JuanCruzz7/Sistema_de_deteccion_de_accidentes_vehiculares/Sistema de detección de accidentes vehiculares/Imágenes/6 - Implementación de pack de baterías.jpeg

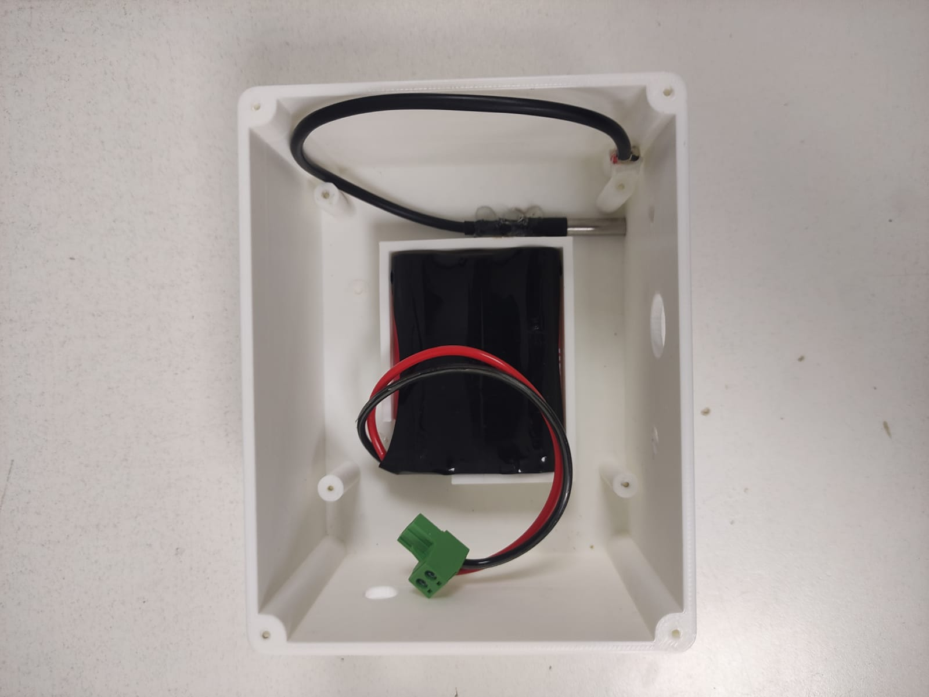
Sistema de detección de accidentes vehiculares/Imágenes/6 - Implementación de pack de baterías.jpeg
