JuanCruzz7/Sistema_de_deteccion_de_accidentes_vehiculares/Sistema de detección de accidentes vehiculares/Imágenes/10 - Comunicación serie - segundo prototipo de PCB.jpeg

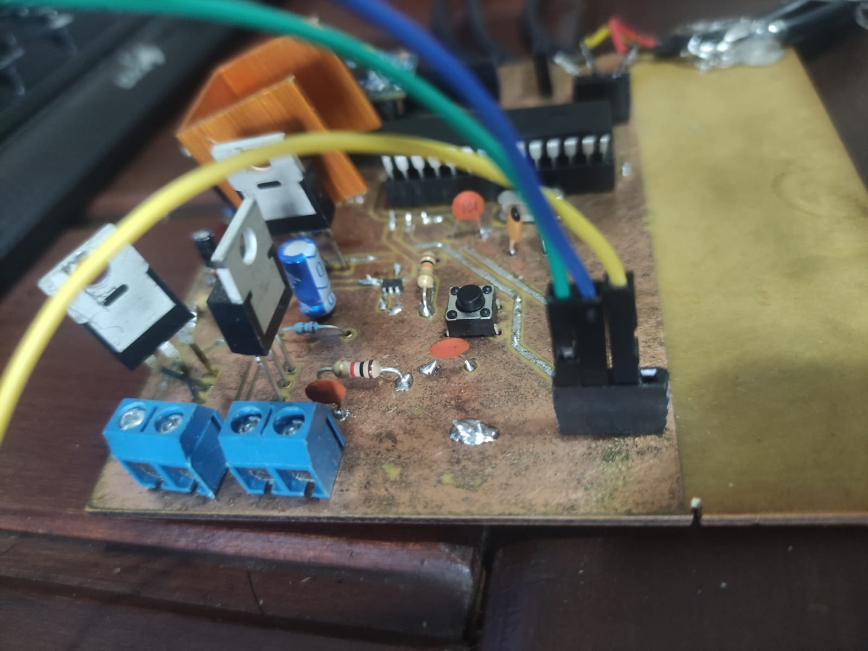
Sistema de detección de accidentes vehiculares/Imágenes/10 - Comunicación serie - segundo prototipo de PCB.jpeg
