JuanCruzz7/Sistema_de_deteccion_de_accidentes_vehiculares/Sistema de detección de accidentes vehiculares/Imágenes/13 - Antena GPS.jpeg

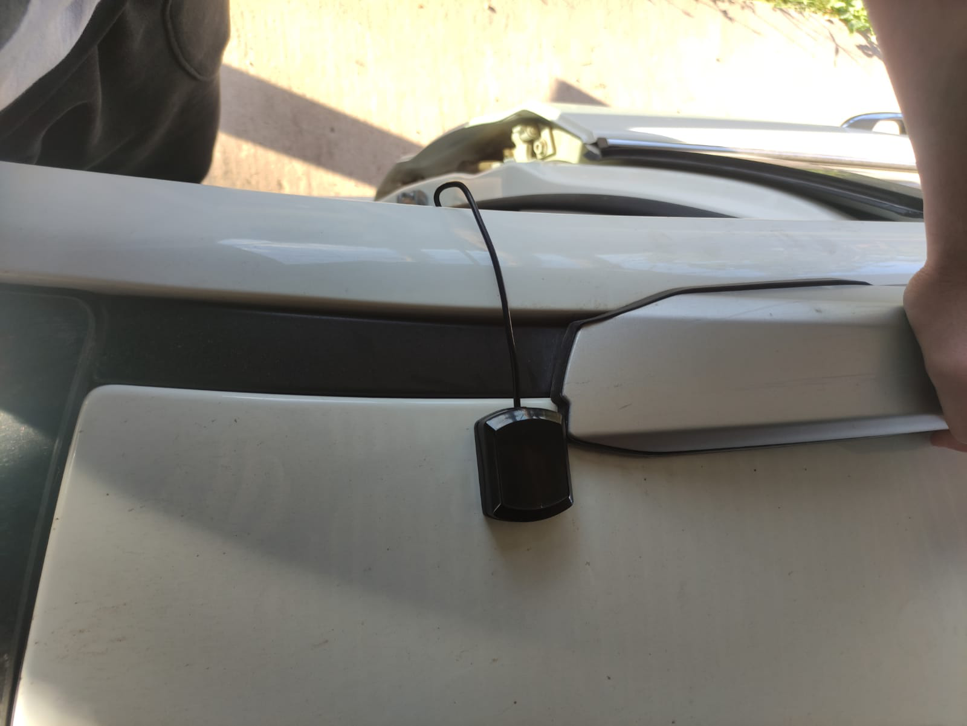
Sistema de detección de accidentes vehiculares/Imágenes/13 - Antena GPS.jpeg
