JuanCruzz7/Sistema_de_deteccion_de_accidentes_vehiculares/Sistema de detección de accidentes vehiculares/Imágenes/1 - Proyecto terminado y ensamblado - vista superior.jpeg

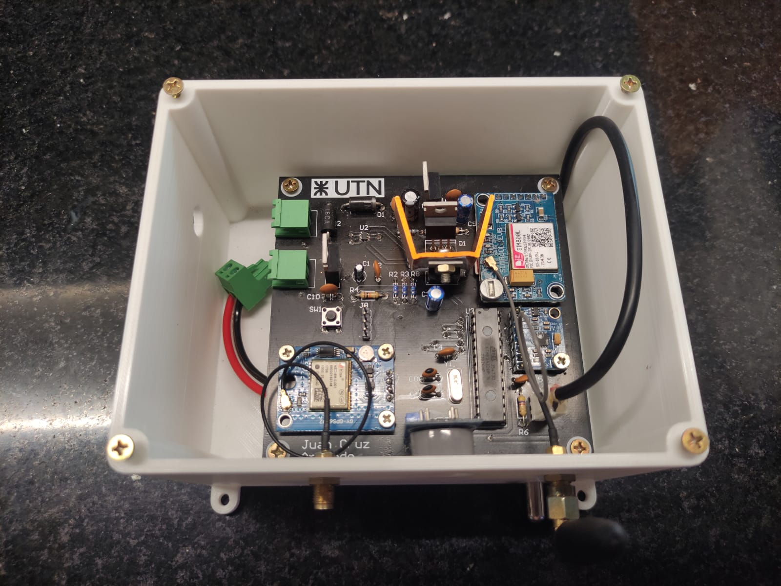
Sistema de detección de accidentes vehiculares/Imágenes/1 - Proyecto terminado y ensamblado - vista superior.jpeg
