JuanCruzz7/Sistema_de_deteccion_de_accidentes_vehiculares/Sistema de detección de accidentes vehiculares/Imágenes/2 - Proyecto terminado y ensamblado.jpeg

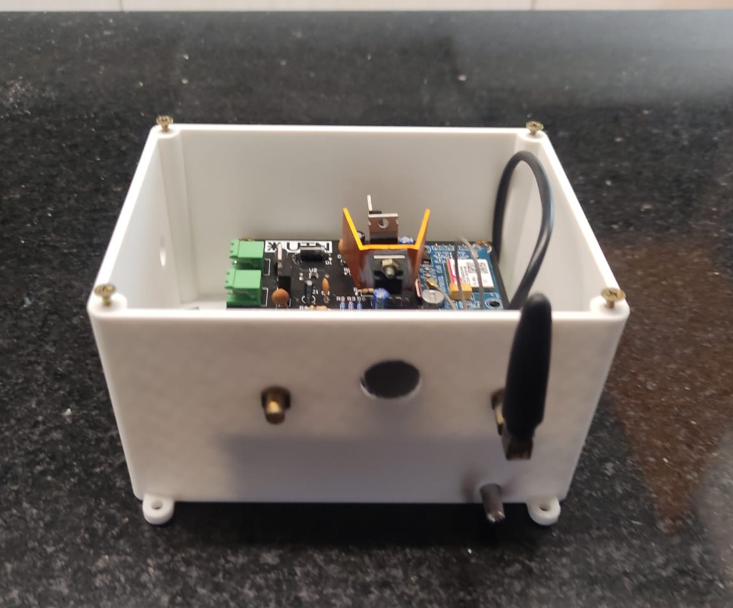
Sistema de detección de accidentes vehiculares/Imágenes/2 - Proyecto terminado y ensamblado.jpeg
