JuanCruzz7/Sistema_de_deteccion_de_accidentes_vehiculares/Sistema de detección de accidentes vehiculares/Imágenes/5 - Carcaza fabricada.jpeg

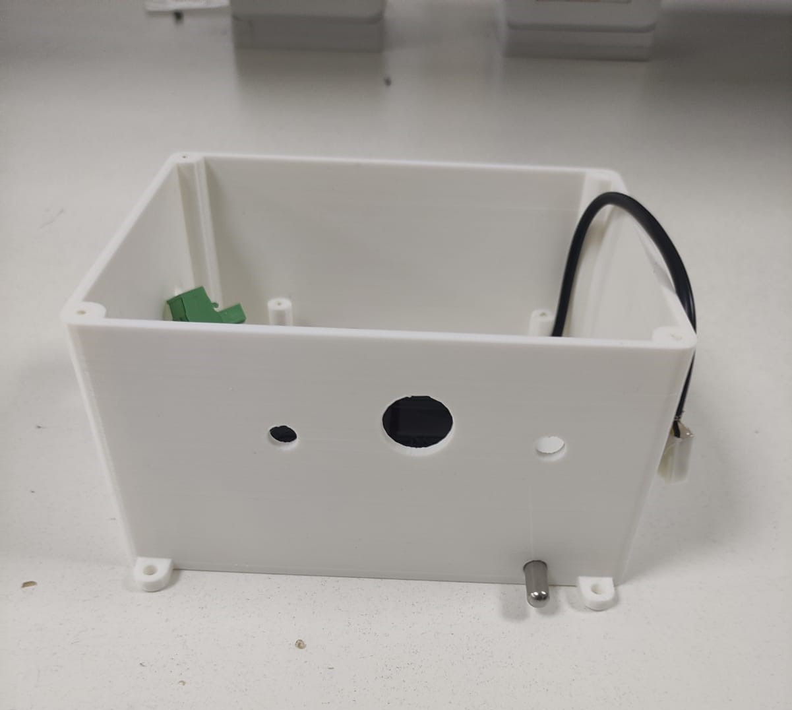
Sistema de detección de accidentes vehiculares/Imágenes/5 - Carcaza fabricada.jpeg
