JuanCruzz7/Sistema_de_deteccion_de_accidentes_vehiculares/Sistema de detección de accidentes vehiculares/Imágenes/12 - Test de alimentación - primer prototipo PCB.jpeg

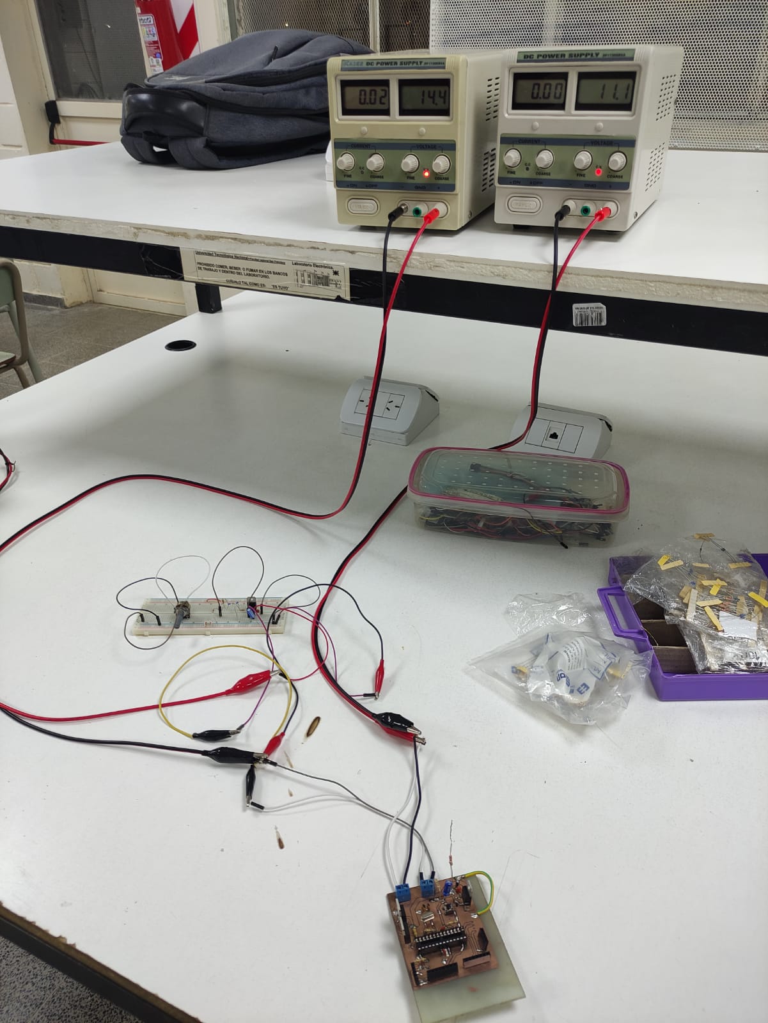
Sistema de detección de accidentes vehiculares/Imágenes/12 - Test de alimentación - primer prototipo PCB.jpeg
